honeypieio/five-band-eq/simulation/active-five-band-eq.asc

C1: cap; 470n
C2: cap; 220n
C3: cap; 220n
C4: cap; 100n
C5: cap; 100n
C6: cap; 100n
C7: cap; 22n
C8: cap; 47n
C9: cap; 22n
C10: cap; 100µ; Rser=8
C11: cap; 1µ
C12: cap; 100µ; Rser=8
C13: cap; 22n
C14: cap; 22n
C15: cap; 2.2n
C16: cap; 100n
D1: diode
D2: diode
Q1: npn; BC547B
Q2: npn; BC547B
Q3: npn; BC547B
Q4: npn; BC547B
Q5: npn; BC547B
Q6: npn; BC547B
Q7: npn; BC547B
Q8: npn; BC547B
Q9: npn; BC547B
Q10: npn; BC547B
R1: res; 9.1k
R2: res; 2.2k
R3: res; 270
R4: res; 680
R5: res; 10k
R6: res; 9.1k
R7: res; 10k
R8: res; 50k
R9: res; 10k
R10: res; 2.2k
R11: res; 270
R12: res; 680
R13: res; 10k
R14: res; 10k
R15: res; 50k
R16: res; 10k
R17: res; 9.1k
R18: res; 2.2k
R19: res; 220
R20: res; 680
R21: res; 10k
R22: res; 22k
R23: res; 50k
R24: res; 10k
R25: res; 22k
R26: res; 50k
R27: res; 50k
R28: res; 50k; tol=100k
R29: res; 1k
R30: res; 9.1k
R31: res; 2.2k
R32: res; 220
R33: res; 680
R34: res; 10k
R35: res; 10k
R36: res; 33k
R37: res; 50k
R38: res; 5k
R39: res; 9.1k
R40: res; 2.2k
R41: res; 220
R42: res; 680
R43: res; 10k
R44: res; 22k
R45: res; 50k
R46: res; 50k
R47: res; 10k
R48: res; 4k
R49: res; 2.2k
R50: res; 1
R51: res; 100k
R52: res; 1
R53: res; 1Meg
U1: opamp
U2: opamp
U3: opamp
U4: opamp
V2: voltage; 15
V3: voltage; SINE(0 100m 1k); AC ac
Named nets: 0
;.tran 0 10m 5m
.ac dec 1000 20 20k
MIDDLE
TREBLE
PRESENCE
.include opamp.sub
BASS
BRILLIANCE
R46, 45 = 100k POT
R27, 23 = 100k POT
R28, 15 = 100k POT
R26, 8 = 100k POT
R37 = 100k POT
R50 = 100k POT
R51, 52 = 100k POT
